lightaprs/LightTracker-Plus-1.0/images/lightracker_plus_with_case_screen.jpg

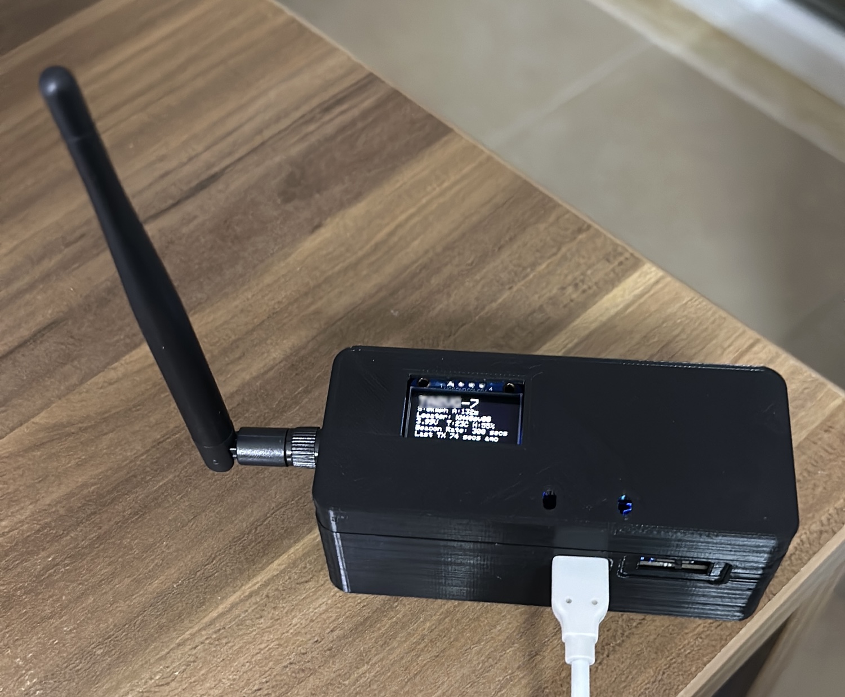
images/lightracker_plus_with_case_screen.jpg
